lodefmode/moviecart/kernel/color_chart/color_chart_ntsc.png

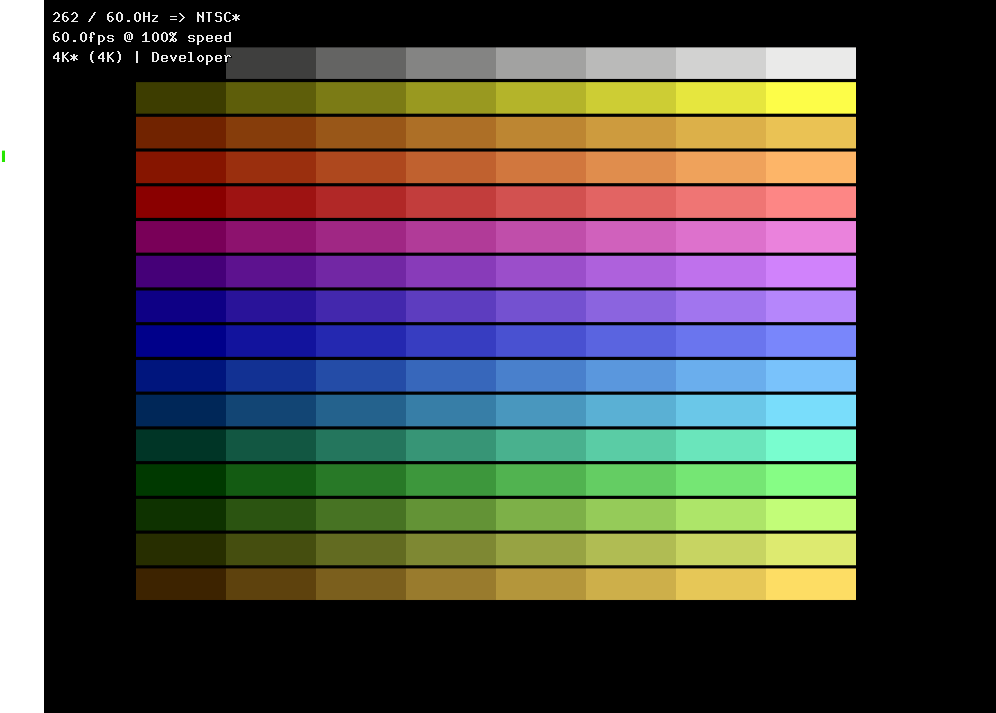
kernel/color_chart/color_chart_ntsc.png
