lodefmode/moviecart/encoder/cpu/ColorizeTOP.cpp

/* Shared Use License: This file is owned by Derivative Inc. (Derivative)
* and can only be used, and/or modified for use, in conjunction with
* Derivative's TouchDesigner software, and only if you are a licensee who has
* accepted Derivative's TouchDesigner license or assignment agreement
* (which also govern the use of this file). You may share or redistribute
* a modified version of this file provided the following conditions are met:
*
* 1. The shared file or redistribution must retain the information set out
* above and this list of conditions.
* 2. Derivative's name (Derivative Inc.) or its trademarks may not be used
* to endorse or promote products derived from this file without specific
* prior written permission from Derivative.
*/

#include "ColorizeTOP.h"

#include <stdio.h>
#include <string.h>


// These functions are basic C function, which the DLL loader can find
// much easier than finding a C++ Class.
// The DLLEXPORT prefix is needed so the compile exports these functions from the .dll
// you are creating
extern "C"
{

DLLEXPORT
void
FillTOPPluginInfo(TOP_PluginInfo *info)
{
	// This must always be set to this constant
	info->apiVersion = TOPCPlusPlusAPIVersion;

	// Change this to change the executeMode behavior of this plugin.
	info->executeMode = TOP_ExecuteMode::CPUMem;

	// The opType is the unique name for this TOP. It must start with a
	// capital A-Z character, and all the following characters must lower case
	// or numbers (a-z, 0-9)
	info->customOPInfo.opType->setString("Colorize");

	// The opLabel is the text that will show up in the OP Create Dialog
	info->customOPInfo.opLabel->setString("Colorize");

	// Will be turned into a 3 letter icon on the nodes
	info->customOPInfo.opIcon->setString("CLZ");

	// Information about the author of this OP
	info->customOPInfo.authorName->setString("Lodef Mode");
	info->customOPInfo.authorEmail->setString("lodef.mode@gmail.com");

	// This TOP works with 1 inputs connected
	info->customOPInfo.minInputs = 1;
	info->customOPInfo.maxInputs = 1;
}

DLLEXPORT
TOP_CPlusPlusBase*
CreateTOPInstance(const OP_NodeInfo* info, TOP_Context* context)
{
	// Return a new instance of your class every time this is called.
	// It will be called once per TOP that is using the .dll
	return new ColorizeTOP(info, context);
}

DLLEXPORT
void
DestroyTOPInstance(TOP_CPlusPlusBase* instance, TOP_Context *context)
{
	// Delete the instance here, this will be called when
	// Touch is shutting down, when the TOP using that instance is deleted, or
	// if the TOP loads a different DLL
	delete (ColorizeTOP*)instance;
}

};

const float	colorScales[3] = {0.299f, 0.587f, 0.114f};

float
colorDist(const float a[3], const float b[3])
{
	float dist =
		(a[0] - b[0])*(a[0] - b[0]) * colorScales[0] +
		(a[1] - b[1])*(a[1] - b[1]) * colorScales[1] +
		(a[2] - b[2])*(a[2] - b[2]) * colorScales[2];
	
	return dist;
}

/////////////////////////////////////////////////////////
/* Adapted from: https://rosettacode.org/wiki/K-d_tree */

 
inline float
dist(struct kd_node_t *a, struct kd_node_t *b)
{
	return colorDist(a->val, b->val);
}

inline void
swap_nodes(struct kd_node_t *x, struct kd_node_t *y) 
{
	kd_node_t	tmp;

	tmp.val[0] = x->val[0];
	tmp.val[1] = x->val[1];
	tmp.val[2] = x->val[2];
	tmp.index = x->index;

	x->val[0] = y->val[0];
	x->val[1] = y->val[1];
	x->val[2] = y->val[2];
	x->index = y->index;

	y->val[0] = tmp.val[0];
	y->val[1] = tmp.val[1];
	y->val[2] = tmp.val[2];
	y->index = tmp.index;
}
 
 
/* see quickselect method */
static struct kd_node_t*
find_median(struct kd_node_t *start, struct kd_node_t *end, int idx)
{
    if (end <= start)
		return nullptr;

    if (end == start + 1)
        return start;
 
    struct kd_node_t *p, *store, *md = start + (end - start) / 2;

    while (1) 
	{
		float pivot = md->val[idx];
 
        swap_nodes(md, end - 1);
        for (store = p = start; p < end; p++) 
		{
            if (p->val[idx] < pivot) 
			{
                if (p != store)
                    swap_nodes(p, store);
                store++;
            }
        }
        swap_nodes(store, end - 1);
 
        /* median has duplicate values */
        if (store->val[idx] == md->val[idx])
            return md;
 
        if (store > md)
			end = store;
        else
			start = store;
    }
}
 
static struct kd_node_t*
make_tree(struct kd_node_t *t, long len, int i)
{
    struct kd_node_t *n;
 
    if (!len)
		return 0;
 
    if ((n = find_median(t, t + len, i))) 
	{
        i = (i + 1) % MAX_DIM;
        n->left  = make_tree(t, n - t, i);
        n->right = make_tree(n + 1, t + len - (n + 1), i);
    }
    return n;
}
 
 
static void
nearest(struct kd_node_t *root, struct kd_node_t *nd, int i,
        struct kd_node_t **best, float *best_dist)
{
    float d, dx, dx2;
 
    if (!root)
		return;

    d = dist(root, nd);
    dx = root->val[i] - nd->val[i];

    dx2 = dx * dx;

	dx2 *= colorScales[i];

    if (!*best || d < *best_dist) 
	{
        *best_dist = d;
        *best = root;
    }
 
    /* if chance of exact match is high */
    if (!*best_dist)
		return;
 
    if (++i >= MAX_DIM)
		i = 0;
 
    nearest(dx > 0 ? root->left : root->right, nd, i, best, best_dist);

    if (dx2 >= *best_dist)
		return;

    nearest(dx > 0 ? root->right : root->left, nd, i, best, best_dist);
}
 
void
ColorizeTOP::setup_kdtree(Array2D<float[3]>& fpal, int palSize)
{
	if (palSize > 256)
		palSize = 256;

    for (int i=0; i<palSize; i++)
    {
		kd_node_t	&n = kdtree[i];

        n.val[0] = fpal(i,0)[0];
        n.val[1] = fpal(i,0)[1];
        n.val[2] = fpal(i,0)[2];
		n.index = i;
	}

    kdtree_root = make_tree(kdtree, palSize, 0);
}

static int
search_kdtree(float r, float g, float b, kd_node_t* root)
{
	kd_node_t	n;

	n.val[0] = r;
	n.val[1] = g;
	n.val[2] = b;

    struct kd_node_t *found = nullptr;
    float best_dist;

    nearest(root, &n, 0, &found, &best_dist);

	if (found)
		return found->index;

	return -1;
}

/*              end of kd -tree                        */
/////////////////////////////////////////////////////////

void
ColorizeTOP::buildColourMap() 
{
    for (int r = 0; r < 256; r++) 
	{
        for (int g = 0; g < 256; g++) 
		{
            for (int b = 0; b < 256; b++) 
			{
                float rr = r / 255.0f;
                float gg = g / 255.0f;
                float bb = b / 255.0f;
                                
				int		minIndex = search_kdtree(rr, gg, bb, kdtree_root);

                myColorLookup[r][g][b] = minIndex;
            }
        }
    }
}

unsigned char
rubik_palette[] =
{
  0x00, 0x9b, 0x48,
  0xff, 0xff, 0xff,
  0xb7, 0x12, 0x34,
  0xff, 0xd5, 0x00,
  0x00, 0x46, 0xad,
  0xff, 0x58, 0x00
};


/*
 GIMP Palette
 Name: HW Atari 2600 (PAL)
 Columns: 16
 # https://en.wikipedia.org/wiki/List_of_video_game_console_palettes#Atari_2600
   0   0   0    0+1+14+15, 0
  40  40  40    0+1+14+15, 2
  80  80  80    0+1+14+15, 4
 116 116 116    0+1+14+15, 6
 148 148 148    0+1+14+15, 8
 180 180 180    0+1+14+15, 10
 208 208 208    0+1+14+15, 12
 236 236 236    0+1+14+15, 14
 128  88   0    2, 0
 148 112  32    2, 2
 168 132  60    2, 4
 188 156  88    2, 6
 204 172 112    2, 8
 220 192 132    2, 10
 236 208 156    2, 12
 252 224 176    2, 14
  68  92   0    3, 0
  92 120  32    3, 2
 116 144  60    3, 4
 140 172  88    3, 6
 160 192 112    3, 8
 176 212 132    3, 10
 196 232 156    3, 12
 212 252 176    3, 14
 112  52   0    4, 0
 136  80  32    4, 2
 160 104  60    4, 4
 180 132  88    4, 6
 200 152 112    4, 8
 220 172 132    4, 10
 236 192 156    4, 12
 252 212 176    4, 14
   0 100  20    5, 0
  32 128  52    5, 2
  60 152  80    5, 4
  88 176 108    5, 6
 112 196 132    5, 8
 132 216 156    5, 10
 156 232 180    5, 12
 176 252 200    5, 14
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
 
 */

/*
 GIMP Palette
 Name: HW Atari 2600 (SECAM)
 Columns: 8
 # https://en.wikipedia.org/wiki/List_of_video_game_console_palettes#Atari_2600
   0   0   0     0
  33  33 255     2
 240  60 121     4
 255  80 255     6
 127 255   0     8
 127 255 255     10
 255 255  63     12
 255 255 255     14
 */

unsigned char atari2600pal_palette[] =
{
      0,   0,   0,
     40,  40,  40,
     80,  80,  80,
    116, 116, 116,
    148, 148, 148,
    180, 180, 180,
    208, 208, 208,
    236, 236, 236,

    0,   0,   0,
     40,  40,  40,
     80,  80,  80,
    116, 116, 116,
    148, 148, 148,
    180, 180, 180,
    208, 208, 208,
    236, 236, 236,
    
    128,  88,   0,
    148, 112,  32,
    168, 132,  60,
    188, 156,  88,
    204, 172, 112,
    220, 192, 132,
    236, 208, 156,
    252, 224, 176,
    
    68,  92,   0,
     92, 120,  32,
    116, 144,  60,
    140, 172,  88,
    160, 192, 112,
    176, 212, 132,
    196, 232, 156,
    212, 252, 176,
    
    112,  52,   0,
    136,  80,  32,
    160, 104,  60,
    180, 132,  88,
    200, 152, 112,
    220, 172, 132,
    236, 192, 156,
    252, 212, 176,
    
      0, 100,  20,
     32, 128,  52,
     60, 152,  80,
     88, 176, 108,
    112, 196, 132,
    132, 216, 156,
    156, 232, 180,
    176, 252, 200,
    
    112,   0,  20,
    136,  32,  52,
    160,  60,  80,
    180,  88, 108,
    200, 112, 132,
    220, 132, 156,
    236, 156, 180,
    252, 176, 200,
    
      0,  92,  92,
     32, 116, 116,
     60, 140, 140,
     88, 164, 164,
    112, 184, 184,
    132, 200, 200,
    156, 220, 220,
    176, 236, 236,
    
    112,   0,  92,
    132,  32, 116,
    148,  60, 136,
    168,  88, 156,
    180, 112, 176,
    196, 132, 192,
    208, 156, 208,
    224, 176, 224,
    
      0,  60, 112,
     28,  88, 136,
     56, 116, 160,
     80, 140, 180,
    104, 164, 200,
    124, 184, 220,
    144, 204, 236,
    164, 224, 252,
    
    88,   0, 112,
    108,  32, 136,
    128,  60, 160,
    148,  88, 180,
    164, 112, 200,
    180, 132, 220,
    196, 156, 236,
    212, 176, 252,
    
      0,  32, 112,
     28,  60, 136,
     56,  88, 160,
     80, 116, 180,
    104, 136, 200,
    124, 160, 220,
    144, 180, 236,
    164, 200, 252,
    
     60,   0, 128,
     84,  32, 148,
    108,  60, 168,
    128,  88, 188,
    148, 112, 204,
    168, 132, 220,
    184, 156, 236,
    200, 176, 252,
    
      0,   0, 136,
     32,  32, 156,
     60,  60, 176,
     88,  88, 192,
    112, 112, 208,
    132, 132, 224,
    156, 156, 236,
    176, 176, 252,
    
//      0,   0,   0,
//     40,  40,  40,
//     80,  80,  80,
//    116, 116, 116,
//    148, 148, 148,
//    180, 180, 180,
//    208, 208, 208,
//    236, 236, 236,
//
//      0,   0,   0,
//     40,  40,  40,
//     80,  80,  80,
//    116, 116, 116,
//    148, 148, 148,
//    180, 180, 180,
//    208, 208, 208,
//    236, 236, 236,
};

unsigned char atari2600secam_palette[] =
{
      0,   0,   0,
     33,  33, 255,
    240,  60, 121,
    255,  80, 255,
    127, 255,   0,
    127, 255, 255,
    255, 255,  63,
    255, 255, 255,
};

// stella uInt32 Console::ourNTSCPalette[128] = 
unsigned char
atari2600ntsc_palette[] =
{
  0x00, 0x00, 0x00,
  0x4a, 0x4a, 0x4a,
  0x6f, 0x6f, 0x6f,
  0x8e, 0x8e, 0x8e,
  0xaa, 0xaa, 0xaa,
  0xc0, 0xc0, 0xc0,
  0xd6, 0xd6, 0xd6,
  0xec, 0xec, 0xec,
  0x48, 0x48, 0x00,
  0x69, 0x69, 0x0f,
  0x86, 0x86, 0x1d,
  0xa2, 0xa2, 0x2a,
  0xbb, 0xbb, 0x35,
  0xd2, 0xd2, 0x40,
  0xe8, 0xe8, 0x4a,
  0xfc, 0xfc, 0x54,
  0x7c, 0x2c, 0x00,
  0x90, 0x48, 0x11,
  0xa2, 0x62, 0x21,
  0xb4, 0x7a, 0x30,
  0xc3, 0x90, 0x3d,
  0xd2, 0xa4, 0x4a,
  0xdf, 0xb7, 0x55,
  0xec, 0xc8, 0x60,
  0x90, 0x1c, 0x00,
  0xa3, 0x39, 0x15,
  0xb5, 0x53, 0x28,
  0xc6, 0x6c, 0x3a,
  0xd5, 0x82, 0x4a,
  0xe3, 0x97, 0x59,
  0xf0, 0xaa, 0x67,
  0xfc, 0xbc, 0x74,
  0x94, 0x00, 0x00, 
  0xa7, 0x1a, 0x1a,
  0xb8, 0x32, 0x32,
  0xc8, 0x48, 0x48,
  0xd6, 0x5c, 0x5c,
  0xe4, 0x6f, 0x6f,
  0xf0, 0x80, 0x80,
  0xfc, 0x90, 0x90,
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
};

// random terrain
unsigned char
atari2600randomterrain_palette[] =
{
	0x00,0x00,0x00,
	0x1A,0x1A,0x1A,
	0x39,0x39,0x39,
	0x5B,0x5B,0x5B,
	0x7E,0x7E,0x7E,
	0xA2,0xA2,0xA2,
	0xC7,0xC7,0xC7,
	0xED,0xED,0xED,
	0x19,0x02,0x00,
	0x3A,0x1F,0x00,
	0x5D,0x41,0x00,
	0x82,0x64,0x00,
	0xA7,0x88,0x00,
	0xCC,0xAD,0x00,
	0xF2,0xD2,0x19,
	0xFE,0xFA,0x40,
	0x37,0x00,0x00,
	0x5E,0x08,0x00,
	0x83,0x27,0x00,
	0xA9,0x49,0x00,
	0xCF,0x6C,0x00,
	0xF5,0x8F,0x17,
	0xFE,0xB4,0x38,
	0xFE,0xDF,0x6F,
	0x47,0x00,0x00,
	0x73,0x00,0x00,
	0x98,0x13,0x00,
	0xBE,0x32,0x16,
	0xE4,0x53,0x35,
	0xFE,0x76,0x57,
	0xFE,0x9C,0x81,
	0xFE,0xC6,0xBB,
	0x44,0x00,0x08,
	0x6F,0x00,0x1F,
	0x96,0x06,0x40,
	0xBB,0x24,0x62,
	0xE1,0x45,0x85,
	0xFE,0x67,0xAA,
	0xFE,0x8C,0xD6,
	0xFE,0xB7,0xF6,
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
};

unsigned char
bw2_palette[] =
{
	0, 0, 0,
	255, 255, 255
};

unsigned char
bw4_palette[] =
{
	0, 0, 0,
	85, 85, 85,
	170, 170, 170,
	255, 255, 255
};

unsigned char
rgb_palette[] =
{
	0, 0, 0,
	0, 0, 255,
	0, 255, 0,
	255, 0, 0
};


// https://en.wikipedia.org/wiki/Texas_Instruments_TMS9918#Colors
unsigned char colecovision_palette[16*3] =
{
	0x00, 0x00, 0x00, // transparent	
	0x00, 0x00, 0x00, // black	
	0x0A, 0xAD, 0x1E, // medium green	
	0x34, 0xC8, 0x4C, // light green	
	0x2B, 0x2D, 0xE3, // dark blue	
	0x51, 0x4B, 0xFB, // light blue	
	0xBD, 0x29, 0x25, // dark red	
	0x1E, 0xE2, 0xEF, // cyan	
	0xFB, 0x2C, 0x2B, // medium red	
	0xFF, 0x5F, 0x4C, // light red	
	0xBD, 0xA2, 0x2B, // dark yellow	
	0xD7, 0xB4, 0x54, // light yellow	
	0x0A, 0x8C, 0x18, // dark green	
	0xAF, 0x32, 0x9A, // magenta	
	0xB2, 0xB2, 0xB2, // gray	
	0xFF, 0xFF, 0xFF, // white	
};

inline uint8_t
lookupClosestInPalette(float cellColor[4], Array2D<float[3]>& fpal, const uint8_t lookup[256][256][256]) 
{
    int r = (int)(cellColor[0] * 255.0f);
    int g = (int)(cellColor[1] * 255.0f);
    int b = (int)(cellColor[2] * 255.0f);
    
    int minIndex = lookup[r][g][b];

    // stuff it all back in.

    cellColor[0] = fpal(minIndex,0)[0];
    cellColor[1] = fpal(minIndex,0)[1];
    cellColor[2] = fpal(minIndex,0)[2];
    cellColor[3] = (float)minIndex;

	return minIndex;
}

inline void
findClosest(float cellColor[4], const float* selectColor, const float* backColor)
{
	float distBlack = colorDist(cellColor, backColor);
	float distWhite = colorDist(cellColor, selectColor);

	if (distBlack < distWhite)
	{
		memcpy(cellColor, backColor, sizeof(float)*4);
	}
	else
	{
		memcpy(cellColor, selectColor, sizeof(float)*4);
	}
}

inline void
distributeError(int width, int height, float* mem,
				int x, int y, float* quantError, float ratio)
{
	if (x >=0 && x<width && y>=0 && y<height)
	{
		float* npixel = &mem[4 * (y*width + x)];
		npixel[0] += quantError[0] * ratio;
		npixel[1] += quantError[1] * ratio;
		npixel[2] += quantError[2] * ratio;

		// clamp
		for (int j=0; j<3; j++)
		{
			if (npixel[j] < 0)
				npixel[j] = 0;
			else if (npixel[j] > 1)
				npixel[j] = 1;
		}

	}
}

#define max(a,b)  ((a)>(b) ? (a):(b))
#define min(a,b)  ((a)<(b) ? (a):(b))


enum
{
	Palette_Atari2600NTSC = 0,
	Palette_BW2 = 1,
	Palette_BW4 = 2,
	Palette_RGB = 3,
	Palette_Atari2600RandomTerrain = 4,
	Palette_Rubik = 5,
	Palette_Atari2600PAL = 6,
	Palette_Atari2600SECAM = 7,
	Palette_ColecoVision = 8,
};

enum
{
	Matrix_FloydSteinberg = 0,
	Matrix_JIN = 1,
	Matrix_Atkinson = 2
};

#define PAL(palette) \
    pal = palette; \
    palSize = sizeof(palette) / 3;

void
getPalette(int palette, unsigned char* &pal, int &palSize)
{
	switch(palette)
	{
		case Palette_Atari2600NTSC:
		default:
			pal = PAL(atari2600ntsc_palette);
			break;

		case Palette_Atari2600PAL:
			pal = PAL(atari2600pal_palette);
			break;

		case Palette_Atari2600SECAM:
			pal = PAL(atari2600secam_palette);
			break;

		case Palette_Atari2600RandomTerrain:
			pal = PAL(atari2600randomterrain_palette);
			break;

		case Palette_BW2:
			pal = PAL(bw2_palette);
			break;

		case Palette_BW4:
			pal = PAL(bw4_palette);
			break;

		case Palette_RGB:
			pal = PAL(rgb_palette);
			break;

		case Palette_Rubik:
			pal = PAL(rubik_palette);
			break;

		case Palette_ColecoVision:
			pal = PAL(colecovision_palette);
			break;
	}
}


void
ColorizeTOP::ditherLine(int bidx, int y, bool finalB, int width, int height, int cellSize,
	float* curY, int palSize, float bleed, int matrix,
	bool dither, float* curError,
	float bestError, int colorInc)
{
	float	cellColor[4] = { 1, 1, 1, 0 };
	float	backColor[4];

	backColor[0] = myFPal(bidx,0)[0];
	backColor[1] = myFPal(bidx,0)[1];
	backColor[2] = myFPal(bidx,0)[2];
	backColor[3] = (float)bidx;

	float*	mem = (float*)myMem.getData();

	*curError = 0.0f;

	int xcell = 0;

	for (int x=0; x<width; x++)
	{
		int xpix = x%cellSize;
		float* pixel = &curY[4*x];


		// determine cell color

		if (xpix == 0)	// first pixel of cell
		{
			if (colorInc)
			{
				float	maxError = HUGE_VAL;
				int		bestF = 0;

				// start with best color from previous frame (+2% speed)
				int		startB = myResultColor(xcell, y);

				auto testForeground = [&](int bidx)
				{
					cellColor[0] = myFPal(bidx,0)[0];
					cellColor[1] = myFPal(bidx,0)[1];
					cellColor[2] = myFPal(bidx,0)[2];

					float	cellError = 0;

					for (int x2=0; x2<cellSize; x2++)
					{
						int x3 = x + x2;
						float* npixel = &curY[4*x3];
					
						float distBack = colorDist(npixel, backColor);
						float distWhite = colorDist(npixel, cellColor);

						cellError += min(distBack, distWhite);
						if (cellError >= maxError)
							break;
					}

					if (cellError < maxError)
					{
						maxError = cellError;
						bestF = bidx;
					}
				};

				startB &= ~(colorInc-1); // round down to nearest inc
				for (int b=0; b<palSize; b+=colorInc)
				{
					int		bidx = (startB + b) % palSize;
					testForeground(bidx);
				}

				// now redo rest of hue
				int b2 = bestF & ~(colorInc-1);	// round down to nearest inc
				for (int b=1; b<colorInc; b++)
					testForeground(b2 + b);

				cellColor[0] = myFPal(bestF,0)[0];
				cellColor[1] = myFPal(bestF,0)[1];
				cellColor[2] = myFPal(bestF,0)[2];
				cellColor[3] = bestF;
			}
			else // average
			{
				float	total_weight = 0.0f;

				cellColor[0] = 0.0f;
				cellColor[1] = 0.0f;
				cellColor[2] = 0.0f;


				for (int x2=0; x2<cellSize; x2++)
				{
					int x3 = x + x2;

					float* npixel = &curY[4*x3];
				
					float r = npixel[0];
					float g = npixel[1];
					float b = npixel[2];

					float weight = r*colorScales[0] + g*colorScales[1] + b*colorScales[2];
					//
					// weigh background minimally
					{
						float	dist = colorDist(npixel, backColor);
						weight *= dist;
					}

					cellColor[0] += r*weight;
					cellColor[1] += g*weight;
					cellColor[2] += b*weight;

					total_weight += weight;
				}

				if (total_weight)
				{
					cellColor[0] /= total_weight;
					cellColor[1] /= total_weight;
					cellColor[2] /= total_weight;
				}
			}

			uint8_t i = lookupClosestInPalette(cellColor, myFPal, myColorLookup);
			myResultColor(xcell, y) = i;
			xcell++;
		}

		// now dither
		if (dither)
		{
			float current[3];
			current[0] = pixel[0];
			current[1] = pixel[1];
			current[2] = pixel[2];

			findClosest(pixel, cellColor, backColor);

			*curError += colorDist(current, pixel);
			if (!finalB && *curError >= bestError)
				return;

			if (bleed > 0)
			{
				float quantError[3];
				
				for (int i = 0; i < 3; i++)
					quantError[i] = (current[i] - pixel[i]) * bleed;

				switch(matrix)
				{
					case Matrix_FloydSteinberg:
					default:
						distributeError(width, height, curY, x+1, 0, quantError, 7.0f / 16.0f);

						if (finalB)
						{
							distributeError(width, height, mem, x-1, y+1, quantError, 3.0f / 16.0f);
							distributeError(width, height, mem, x+0, y+1, quantError, 5.0f / 16.0f);
							distributeError(width, height, mem, x+1, y+1, quantError, 1.0f / 16.0f);
						}
						break;

					case Matrix_JIN:
					#if 0
							 -   -   X   7   5 
							 3   5   7   5   3
							 1   3   5   3   1
					 #endif
						distributeError(width, height, curY, x+1, 0, quantError, 7.0f / 48.0f);
						distributeError(width, height, curY, x+2, 0, quantError, 5.0f / 48.0f);

						if (finalB)
						{
							distributeError(width, height, mem, x-2, y+1, quantError, 3.0f / 48.0f);
							distributeError(width, height, mem, x-1, y+1, quantError, 5.0f / 48.0f);
							distributeError(width, height, mem, x+0, y+1, quantError, 7.0f / 48.0f);
							distributeError(width, height, mem, x+1, y+1, quantError, 5.0f / 48.0f);
							distributeError(width, height, mem, x+2, y+1, quantError, 3.0f / 48.0f);

							distributeError(width, height, mem, x-2, y+2, quantError, 1.0f / 48.0f);
							distributeError(width, height, mem, x-1, y+2, quantError, 3.0f / 48.0f);
							distributeError(width, height, mem, x+0, y+2, quantError, 5.0f / 48.0f);
							distributeError(width, height, mem, x+1, y+2, quantError, 3.0f / 48.0f);
							distributeError(width, height, mem, x+2, y+2, quantError, 1.0f / 48.0f);
						}

						break;

					case Matrix_Atkinson: // (partial error distribution 6/8)

					#if 0
						-   X   1   1 
						1   1   1
						-   1
				   #endif

						distributeError(width, height, curY, x+1, 0, quantError, 1.0f / 8.0f);
						distributeError(width, height, curY, x+2, 0, quantError, 1.0f / 8.0f);

						if (finalB)
						{
							distributeError(width, height, mem, x-1, y+1, quantError, 1.0f / 8.0f);
							distributeError(width, height, mem, x+0, y+1, quantError, 1.0f / 8.0f);
							distributeError(width, height, mem, x+1, y+1, quantError, 1.0f / 8.0f);

							distributeError(width, height, mem, x+0, y+2, quantError, 1.0f / 8.0f);
						}
						
						break;

				}

			}
		}
		else
		{
			memcpy(pixel, cellColor, 4*sizeof(float));
		}

	}
}


ColorizeTOP::ColorizeTOP(const OP_NodeInfo* info, TOP_Context* context) :
	myContext(context)
{
	myLastPal = nullptr;
}

ColorizeTOP::~ColorizeTOP()
{
}

void
ColorizeTOP::getGeneralInfo(TOP_GeneralInfo* ginfo, const OP_Inputs* inputs, void* reserved1)
{
	ginfo->cookEveryFrameIfAsked = true;
}

void
ColorizeTOP::execute(TOP_Output* output, const OP_Inputs* inputs, void* reserved1)
{
    bool active = inputs->getParInt("Active") ? true:false;
    int palette = inputs->getParInt("Palette");
    int cellSize = inputs->getParInt("Cellsize");

    bool dither = inputs->getParInt("Dither") ? true:false;
    float bleed = (float)inputs->getParDouble("Bleed");
    bool bleedSearch = inputs->getParInt("Bleedsearch") ? true:false;

    int matrix = inputs->getParInt("Matrix");

    int colorSearch = inputs->getParInt("Colorsearch");
	int colorInc = 1;

	switch(colorSearch)
	{
		case 0: colorInc = 0; break;
		case 1: colorInc = 8; break;
		case 2: colorInc = 4; break;
		case 3: colorInc = 2; break;
		case 4: colorInc = 1; break;
	}

    if (palette != Palette_Atari2600NTSC &&
	    palette != Palette_Atari2600RandomTerrain &&
        palette != Palette_Atari2600PAL)
	{
		if (colorInc > 1)
			colorInc = 1;
	}


	// cache palette

    unsigned char*	pal;
    int             palSize;
    getPalette(palette, pal, palSize);
    if (pal != myLastPal)
    {
        myLastPal = pal;
        myFPal.setSize(palSize, 1);

        for (int i=0; i<palSize; i++)
        {
            myFPal(i, 0)[0] = pal[3*i + 0] / 255.0f;
            myFPal(i, 0)[1] = pal[3*i + 1] / 255.0f;
            myFPal(i, 0)[2] = pal[3*i + 2] / 255.0f;
        }

        setup_kdtree(myFPal, palSize);
        buildColourMap();
    }

	// active and input connected?

    if (!active)
        return;
	if (inputs->getNumInputs() < 1)
		return;
	const OP_TOPInput* top = inputs->getInputTOP(0);
	if (!top)
		return;


	// download input

	OP_TOPInputDownloadOptions opts;
	opts.pixelFormat = OP_PixelFormat::RGBA32Float;
	OP_SmartRef<OP_TOPDownloadResult> downRes = top->downloadTexture(opts, nullptr);

	if (downRes)
	{
		int width = downRes->textureDesc.width;
		int height = downRes->textureDesc.height;
		setupStorage(width, height, cellSize);

		// the getData() call on OP_TOPDownloadResult will stall until the download is finished.
		memcpy((float*)myMem.getData(), downRes->getData(), width * height * 4 * sizeof(float));



		auto finishLine = [&](int y, int bidx, float* curY)
		{
			float	curError;
			bool	finalB = true;

			ditherLine(bidx, y, finalB, width, height, cellSize, curY, palSize, bleed,
							 matrix, dither, &curError, HUGE_VAL, colorInc);
		};

		if (!colorInc)
		{
			myResultBK.zero();

			for (int y = 0; y < height; y++)
			{
				float* curY = myMem(0, y);
				int		bidx = 0;
				finishLine(y, bidx, curY);
			}
		}
		else
		{

			for (int y = 0; y < height; y++)
			{
				float* curY = myMem(0, y);
				
				int		bestB = 0;
				float	bestError = HUGE_VAL;

				auto testLine = [&](int bidx)
				{
					float	curError;
					bool	finalB = false;
					float	lbleed = bleedSearch ? bleed : 0.0f;

					memcpy((float*)myMemBackup.getData(), curY, width*4 * sizeof(float));
					ditherLine(bidx, y, finalB, width, height, cellSize, (float*)myMemBackup.getData(), palSize,
							 lbleed, matrix, dither, &curError, bestError, colorInc);

					if (curError < bestError)
					{
						bestError = curError;
						bestB = bidx;
					}
				};

				{
					// start with best color from previous frame
					int		startB = (int)(myResultBK(0, y)[3]);

					startB &= ~(colorInc-1);	// round down to nearest inc

					for (int b=0; b<palSize; b+=colorInc)
					{
						int		bidx = (startB + b) % palSize;
						testLine(bidx);
					}

					// now redo rest of hue
					int b2 = bestB & ~(colorInc-1);	// round down to nearest inc

					for (int b=1; b<colorInc; b++)
					{
						int		bidx = b2 + b;
						testLine(bidx);
					}
				}

				// redo best color
				{
					int		bidx = bestB;
					finishLine(y, bidx, curY);

					myResultBK(0, y)[0] = myFPal(bidx,0)[0];
					myResultBK(0, y)[1] = myFPal(bidx,0)[1];
					myResultBK(0, y)[2] = myFPal(bidx,0)[2];
					myResultBK(0, y)[3] = (float)bidx;
				}
			}
		}

		// now fill in output

		{
			int size = width * height * 4 * sizeof(uint8_t);

			OP_SmartRef<TOP_Buffer> buf = myContext->createOutputBuffer(size, TOP_BufferFlags::None, nullptr);

			uint8_t* destMem = (uint8_t*)buf->data;
			storeResults(destMem, cellSize);


			TOP_UploadInfo info;

			info.textureDesc.width = width;
			info.textureDesc.height = height;
			info.textureDesc.texDim = OP_TexDim::e2D;
			info.textureDesc.pixelFormat = OP_PixelFormat::BGRA8Fixed;

			info.colorBufferIndex = 0;
			output->uploadBuffer(&buf, info, nullptr);
		}
	}
}

void
ColorizeTOP::setupStorage(int outputWidth, int outputHeight, int cellSize)
{
	myResultBK.setSize(1, outputHeight);
	myMem.setSize(outputWidth, outputHeight);
	myMemBackup.setSize(outputWidth, 1);

	outputWidth /= cellSize;
	if (outputWidth < 1)
		outputWidth = 1;

	myResultGraph.setSize(outputWidth, outputHeight);
	myResultColor.setSize(outputWidth, outputHeight);
}

void
ColorizeTOP::storeResults(uint8_t *destMem, int cellSize)
{
	int outputWidth = myResultGraph.getWidth();
	int	outputHeight = myResultGraph.getHeight();

	for (int y = 0; y<outputHeight; y++)
	{
		int	bidx = (int)myResultBK(0, y)[3];

		for (int x=0; x<outputWidth; x++)
		{
			const float* pixel = myMem(x*cellSize, y);

			// take next cellSize rgb bits for dither
			uint8_t val = 0;

			uint8_t* destPixel = &destMem[4 * cellSize * (y*outputWidth + x)];


			for (int i = 0; i < cellSize; i++, destPixel += 4, pixel +=4)
			{
				destPixel[0] = uint8_t(pixel[2] * 255.0f);
				destPixel[1] = uint8_t(pixel[1] * 255.0f);
				destPixel[2] = uint8_t(pixel[0] * 255.0f);
				destPixel[3] = uint8_t(pixel[3]);

				val <<= 1;

				// only store non-backcolor in this array
				if (destPixel[3] != bidx)
				{
					val |= 1;

					// set alpha to solid
					destPixel[3] = 255;
				}
				else
				{
					// turn off background

					destPixel[0] = 0;
					destPixel[1] = 0;
					destPixel[2] = 0;
					destPixel[3] = 0;
				}

			}

			myResultGraph(x, y) = val;
		}
	}
}

int32_t
ColorizeTOP::getNumInfoCHOPChans(void *reserved1)
{
	return 0;
}

void
ColorizeTOP::getInfoCHOPChan(int32_t index, OP_InfoCHOPChan* chan, void* reserved1)
{
}

bool		
ColorizeTOP::getInfoDATSize(OP_InfoDATSize* infoSize, void* reserved1)
{
	infoSize->rows = myResultGraph.getHeight();
	infoSize->cols = myResultGraph.getWidth() + myResultColor.getWidth() + 4;		// graph, color,  bkground

	// Setting this to false means we'll be assigning values to the table
	// one row at a time. True means we'll do it one column at a time.
	infoSize->byColumn = false;
	return true;
}

void
ColorizeTOP::getInfoDATEntries(int32_t index,
								int32_t nCols,
								OP_InfoDATEntries* entries,
								void *reserved1)
{
	// It's safe to use static buffers here because TouchDesigner will make it's own
	// copies of the strings immediately after this call returns
	// (so the buffers can be reuse for each column/row)
	static char intBuffer[256][4];
	static bool first = true;
	if (first)
	{
		for (int i=0; i<256; i++)
#ifdef _WIN32
			sprintf_s(intBuffer[i], "%d", i);
#else
			snprintf(intBuffer[i], 4, "%d", i);
#endif
		first = false;
	}

	int y = myResultColor.getHeight() - index - 1; // reverse


	int offset = 0;

	// graph
	for (int i=0; i<myResultGraph.getWidth(); i++)
	{
		int x = i;
		int v = myResultGraph(x, y);

		entries->values[offset++]->setString(intBuffer[v]);
	}

	// color

	for (int i=0; i<myResultColor.getWidth(); i++)
	{
		int x = i;
		int v = myResultColor(x, y);

		// top 7 bits only
		v <<= 1;

		entries->values[offset++]->setString(intBuffer[v]);
	}


	// color bk

	{
		int v = (int)myResultBK(0, y)[3];

		// top 7 bits only
		v <<= 1;

		entries->values[offset++]->setString(intBuffer[v]);

		for (int i=0; i<3; i++)
		{
			float	f = myResultBK(0, y)[i];
			char	fltBuffer[64];

#ifdef _WIN32
			sprintf_s(fltBuffer, "%g", f);
#else
			snprintf(fltBuffer, 4, "%g", f);
#endif

			entries->values[offset++]->setString(fltBuffer);
		}
	}


}

void
ColorizeTOP::setupParameters(OP_ParameterManager* manager, void *reserved)
{
	{
		OP_NumericParameter  sp;

		sp.name = "Active";
		sp.label = "Active";
		sp.defaultValues[0] = 1;

		manager->appendToggle(sp);
	}

	{
		OP_StringParameter  sp;

		sp.name = "Palette";
		sp.label = "Palette";

		constexpr int	numItems = 9;

		const char *names[numItems] = 
		{
			"Atari2600ntsc",
			"Bw2",
			"Bw4",
			"Rgb",
			"Atari2600randomterrain",
			"Rubik",
			"Atari2600pal",
			"Atari2600secam",
			"Colecovision"
		};

		const char *labels[numItems] = 
		{
			"Atari 2600 NTSC",
			"B/W 2",
			"B/W 4",
			"RGB",
			"Atari 2600 Random Terrain",
			"Rubik",
			"Atari 2600 PAL",
			"Atari 2600 SECAM",
			"ColecoVision"
		};

		manager->appendMenu(sp, numItems, names, labels);
	}
	
	{
		OP_NumericParameter  sp;

		sp.name = "Cellsize";
		sp.label = "Cell Size";

		sp.defaultValues[0] = 8;

		sp.minValues[0] = 1;
		sp.clampMins[0] = true;

		sp.minSliders[0] = 1;
		sp.maxSliders[0] = 16;

		manager->appendInt(sp);
	}


	{
		OP_NumericParameter  sp;

		sp.name = "Dither";
		sp.label = "Dither";

		manager->appendToggle(sp);
	}

	{
		OP_NumericParameter  sp;

		sp.name = "Colorsearch";
		sp.label = "Color Search";

		sp.defaultValues[0] = 2;

		sp.minValues[0] = 0;
		sp.maxValues[0] = 4;

		sp.clampMins[0] = true;
		sp.clampMaxes[0] = true;

		sp.minSliders[0] = 0;
		sp.maxSliders[0] = 4;

		manager->appendInt(sp);
	}

	{
		OP_NumericParameter  sp;

		sp.name = "Bleed";
		sp.label = "Bleed";

		sp.defaultValues[0] = 1;

		manager->appendFloat(sp);
	}

	{
		OP_NumericParameter  sp;

		sp.name = "Bleedsearch";
		sp.label = "Bleed During Search";
		sp.defaultValues[0] = 0;

		manager->appendToggle(sp);
	}

	{
		OP_StringParameter  sp;

		sp.name = "Matrix";
		sp.label = "Matrix";

		const char *names[3] = { "Floydsteinberg", "Jin", "Atkinson" };
		const char *labels[3] = { "Floyd/Steinberg", "JIN", "Atkinson" };

		manager->appendMenu(sp, 3, names, labels);
	}

}

void
ColorizeTOP::pulsePressed(const char* name, void *reserved1)
{
}
