lodefmode/moviecart/firmware/osd.h

// OSD labels
const uint8_t brightLabelEven[] = 
{ 
	0, 0, 0, 0, 0,
	0, 0, 0, 0, 0,
	0, 0, 0, 0, 0,
	0, 225, 48, 12, 252,
	6, 140, 231, 96, 0,
	0, 113, 48, 12, 96,
	6, 140, 192, 96, 0,
	0, 225, 49, 15, 96,
	6, 152, 195, 96, 0,
	0, 49, 48, 12, 96,
	6, 140, 231, 96, 0,
	0, 225, 48, 12, 96,
	0, 0, 0, 0, 0,
	0, 0, 0, 0, 0
};

const uint8_t brightLabelOdd[] =
{
	0, 0, 0, 0, 0,
	0, 0, 0, 0, 0,
	7, 252, 126, 99, 0,
	0, 113, 48, 12, 96,
	6, 140, 192, 96, 0,
	0, 97, 49, 12, 96,
	7, 248, 223, 224, 0,
	0, 113, 49, 12, 96,
	6, 156, 195, 96, 0,
	0, 113, 48, 12, 96,
	7, 142, 127, 96, 0,
	0, 0, 0, 0, 0,
	0, 0, 0, 0, 0,
	0, 0, 0, 0, 0
};

const uint8_t volumeLabelEven[] =
{
	0, 0, 0, 0, 0,
	0, 0, 0, 0, 0,
	0, 0, 0, 0, 0,
	0, 199, 192, 14, 254,
	113, 112, 99, 112, 0,
	0, 140, 192, 14, 192,
	51, 48, 99, 240, 0,
	0, 28, 192, 15, 254,
	31, 48, 99, 240, 0,
	0, 12, 192, 15, 192,
	30, 112, 119, 176, 0,
	0, 7, 252, 12, 254,
	0, 0, 0, 0, 0,
	0, 0, 0, 0, 0
};

const uint8_t volumeLabelOdd[] =
{
	0, 0, 0, 0, 0,
	0, 0, 0, 0, 0,
	97, 224, 99, 112, 0,
	0, 142, 192, 14, 192,
	51, 112, 99, 112, 0,
	0, 28, 192, 15, 192,
	59, 48, 99, 240, 0,
	0, 28, 192, 15, 192,
	30, 112, 99, 176, 0,
	0, 14, 192, 13, 192,
	14, 224, 62, 48, 0,
	0, 0, 0, 0, 0,
	0, 0, 0, 0, 0,
	0, 0, 0, 0, 0
};

// Level bars
// 8 rows *5 columns = 40
const uint8_t levelBarsEvenData[] =
{
	/*0*/
	0, 0, 0, 0, 0,
	0x7f, 0x7f, 0x7f, 0x7f, 0x7f,
	0x41, 0x41, 0x41, 0x41, 0x41,
	0x41, 0x41, 0x41, 0x41, 0x41,
	0x41, 0x41, 0x41, 0x41, 0x41,
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
	0x7f, 0x7f, 0x41, 0x41, 0x41,
	0x7f, 0x41, 0x41, 0x41, 0x41,
	0x7f, 0x7f, 0x41, 0x41, 0x41,
	0x7f, 0x41, 0x41, 0x41, 0x41,
	0x7f, 0x7f, 0x7f, 0x7f, 0x7f,
	0, 0, 0, 0, 0,
	0, 0, 0, 0, 0,
	/*4*/
	0x7f, 0x7f, 0x7f, 0x7f, 0x7f,
	0x7f, 0x7f, 0x41, 0x41, 0x41,
	0x7f, 0x7f, 0x41, 0x41, 0x41,
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
};
