lodefmode/moviecart/firmware/bootloader/mcc_generated_files/pin_manager.h

/**
  PIN MANAGER Generated Driver File

  @Company:
    Microchip Technology Inc.

  @File Name:
    pin_manager.h

  @Summary:
    This is the generated manager file for the PIC24 / dsPIC33 / PIC32MM MCUs device.  This manager
    configures the pins direction, initial state, analog setting.
    The peripheral pin select, PPS, configuration is also handled by this manager.

  @Description:
    This source file provides implementations for PIN MANAGER.
    Generation Information :
        Product Revision  :  PIC24 / dsPIC33 / PIC32MM MCUs - 1.170.0
        Device            :  dsPIC33CK64MC105
    The generated drivers are tested against the following:
        Compiler          :  XC16 v1.61
        MPLAB 	          :  MPLAB X v5.45
*/

/*
    (c) 2020 Microchip Technology Inc. and its subsidiaries. You may use this
    software and any derivatives exclusively with Microchip products.

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
    IN NO EVENT WILL MICROCHIP BE LIABLE FOR ANY INDIRECT, SPECIAL, PUNITIVE,
    INCIDENTAL OR CONSEQUENTIAL LOSS, DAMAGE, COST OR EXPENSE OF ANY KIND
    WHATSOEVER RELATED TO THE SOFTWARE, HOWEVER CAUSED, EVEN IF MICROCHIP HAS
    BEEN ADVISED OF THE POSSIBILITY OR THE DAMAGES ARE FORESEEABLE. TO THE
    FULLEST EXTENT ALLOWED BY LAW, MICROCHIP'S TOTAL LIABILITY ON ALL CLAIMS IN
    ANY WAY RELATED TO THIS SOFTWARE WILL NOT EXCEED THE AMOUNT OF FEES, IF ANY,
    THAT YOU HAVE PAID DIRECTLY TO MICROCHIP FOR THIS SOFTWARE.

    MICROCHIP PROVIDES THIS SOFTWARE CONDITIONALLY UPON YOUR ACCEPTANCE OF THESE
    TERMS.
*/

#ifndef _PIN_MANAGER_H
#define _PIN_MANAGER_H
/**
    Section: Includes
*/
#include <xc.h>

/**
    Section: Device Pin Macros
*/
/**
  @Summary
    Sets the GPIO pin, RA0, high using LATA0.

  @Description
    Sets the GPIO pin, RA0, high using LATA0.

  @Preconditions
    The RA0 must be set to an output.

  @Returns
    None.

  @Param
    None.

  @Example
    <code>
    // Set RA0 high (1)
    IO_RA0_SetHigh();
    </code>

*/
#define IO_RA0_SetHigh()          (_LATA0 = 1)
/**
  @Summary
    Sets the GPIO pin, RA0, low using LATA0.

  @Description
    Sets the GPIO pin, RA0, low using LATA0.

  @Preconditions
    The RA0 must be set to an output.

  @Returns
    None.

  @Param
    None.

  @Example
    <code>
    // Set RA0 low (0)
    IO_RA0_SetLow();
    </code>

*/
#define IO_RA0_SetLow()           (_LATA0 = 0)
/**
  @Summary
    Toggles the GPIO pin, RA0, using LATA0.

  @Description
    Toggles the GPIO pin, RA0, using LATA0.

  @Preconditions
    The RA0 must be set to an output.

  @Returns
    None.

  @Param
    None.

  @Example
    <code>
    // Toggle RA0
    IO_RA0_Toggle();
    </code>

*/
#define IO_RA0_Toggle()           (_LATA0 ^= 1)
/**
  @Summary
    Reads the value of the GPIO pin, RA0.

  @Description
    Reads the value of the GPIO pin, RA0.

  @Preconditions
    None.

  @Returns
    None.

  @Param
    None.

  @Example
    <code>
    uint16_t portValue;

    // Read RA0
    postValue = IO_RA0_GetValue();
    </code>

*/
#define IO_RA0_GetValue()         _RA0
/**
  @Summary
    Configures the GPIO pin, RA0, as an input.

  @Description
    Configures the GPIO pin, RA0, as an input.

  @Preconditions
    None.

  @Returns
    None.

  @Param
    None.

  @Example
    <code>
    // Sets the RA0 as an input
    IO_RA0_SetDigitalInput();
    </code>

*/
#define IO_RA0_SetDigitalInput()  (_TRISA0 = 1)
/**
  @Summary
    Configures the GPIO pin, RA0, as an output.

  @Description
    Configures the GPIO pin, RA0, as an output.

  @Preconditions
    None.

  @Returns
    None.

  @Param
    None.

  @Example
    <code>
    // Sets the RA0 as an output
    IO_RA0_SetDigitalOutput();
    </code>

*/
#define IO_RA0_SetDigitalOutput() (_TRISA0 = 0)
/**
  @Summary
    Sets the GPIO pin, RA1, high using LATA1.

  @Description
    Sets the GPIO pin, RA1, high using LATA1.

  @Preconditions
    The RA1 must be set to an output.

  @Returns
    None.

  @Param
    None.

  @Example
    <code>
    // Set RA1 high (1)
    IO_RA1_SetHigh();
    </code>

*/
#define IO_RA1_SetHigh()          (_LATA1 = 1)
/**
  @Summary
    Sets the GPIO pin, RA1, low using LATA1.

  @Description
    Sets the GPIO pin, RA1, low using LATA1.

  @Preconditions
    The RA1 must be set to an output.

  @Returns
    None.

  @Param
    None.

  @Example
    <code>
    // Set RA1 low (0)
    IO_RA1_SetLow();
    </code>

*/
#define IO_RA1_SetLow()           (_LATA1 = 0)
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
    IO_RD13_SetDigitalInput();
    </code>

*/
#define IO_RD13_SetDigitalInput()  (_TRISD13 = 1)
/**
  @Summary
    Configures the GPIO pin, RD13, as an output.

  @Description
    Configures the GPIO pin, RD13, as an output.

  @Preconditions
    None.

  @Returns
    None.

  @Param
    None.

  @Example
    <code>
    // Sets the RD13 as an output
    IO_RD13_SetDigitalOutput();
    </code>

*/
#define IO_RD13_SetDigitalOutput() (_TRISD13 = 0)
/**
  @Summary
    Sets the GPIO pin, RD8, high using LATD8.

  @Description
    Sets the GPIO pin, RD8, high using LATD8.

  @Preconditions
    The RD8 must be set to an output.

  @Returns
    None.

  @Param
    None.

  @Example
    <code>
    // Set RD8 high (1)
    IO_RD8_SetHigh();
    </code>

*/
#define IO_RD8_SetHigh()          (_LATD8 = 1)
/**
  @Summary
    Sets the GPIO pin, RD8, low using LATD8.

  @Description
    Sets the GPIO pin, RD8, low using LATD8.

  @Preconditions
    The RD8 must be set to an output.

  @Returns
    None.

  @Param
    None.

  @Example
    <code>
    // Set RD8 low (0)
    IO_RD8_SetLow();
    </code>

*/
#define IO_RD8_SetLow()           (_LATD8 = 0)
/**
  @Summary
    Toggles the GPIO pin, RD8, using LATD8.

  @Description
    Toggles the GPIO pin, RD8, using LATD8.

  @Preconditions
    The RD8 must be set to an output.

  @Returns
    None.

  @Param
    None.

  @Example
    <code>
    // Toggle RD8
    IO_RD8_Toggle();
    </code>

*/
#define IO_RD8_Toggle()           (_LATD8 ^= 1)
/**
  @Summary
    Reads the value of the GPIO pin, RD8.

  @Description
    Reads the value of the GPIO pin, RD8.

  @Preconditions
    None.

  @Returns
    None.

  @Param
    None.

  @Example
    <code>
    uint16_t portValue;

    // Read RD8
    postValue = IO_RD8_GetValue();
    </code>

*/
#define IO_RD8_GetValue()         _RD8
/**
  @Summary
    Configures the GPIO pin, RD8, as an input.

  @Description
    Configures the GPIO pin, RD8, as an input.

  @Preconditions
    None.

  @Returns
    None.

  @Param
    None.

  @Example
    <code>
    // Sets the RD8 as an input
    IO_RD8_SetDigitalInput();
    </code>

*/
#define IO_RD8_SetDigitalInput()  (_TRISD8 = 1)
/**
  @Summary
    Configures the GPIO pin, RD8, as an output.

  @Description
    Configures the GPIO pin, RD8, as an output.

  @Preconditions
    None.

  @Returns
    None.

  @Param
    None.

  @Example
    <code>
    // Sets the RD8 as an output
    IO_RD8_SetDigitalOutput();
    </code>

*/
#define IO_RD8_SetDigitalOutput() (_TRISD8 = 0)

/**
    Section: Function Prototypes
*/
/**
  @Summary
    Configures the pin settings of the dsPIC33CK64MC105
    The peripheral pin select, PPS, configuration is also handled by this manager.

  @Description
    This is the generated manager file for the PIC24 / dsPIC33 / PIC32MM MCUs device.  This manager
    configures the pins direction, initial state, analog setting.
    The peripheral pin select, PPS, configuration is also handled by this manager.

  @Preconditions
    None.

  @Returns
    None.

  @Param
    None.

  @Example
    <code>
    void SYSTEM_Initialize(void)
    {
        // Other initializers are called from this function
        PIN_MANAGER_Initialize();
    }
    </code>

*/
void PIN_MANAGER_Initialize (void);



#endif
